aartech-dev/slot-car-track-mapper/electronics/electronics.kicad_sch

## KiCad design electronics/electronics.kicad_sch (2026-09-03)

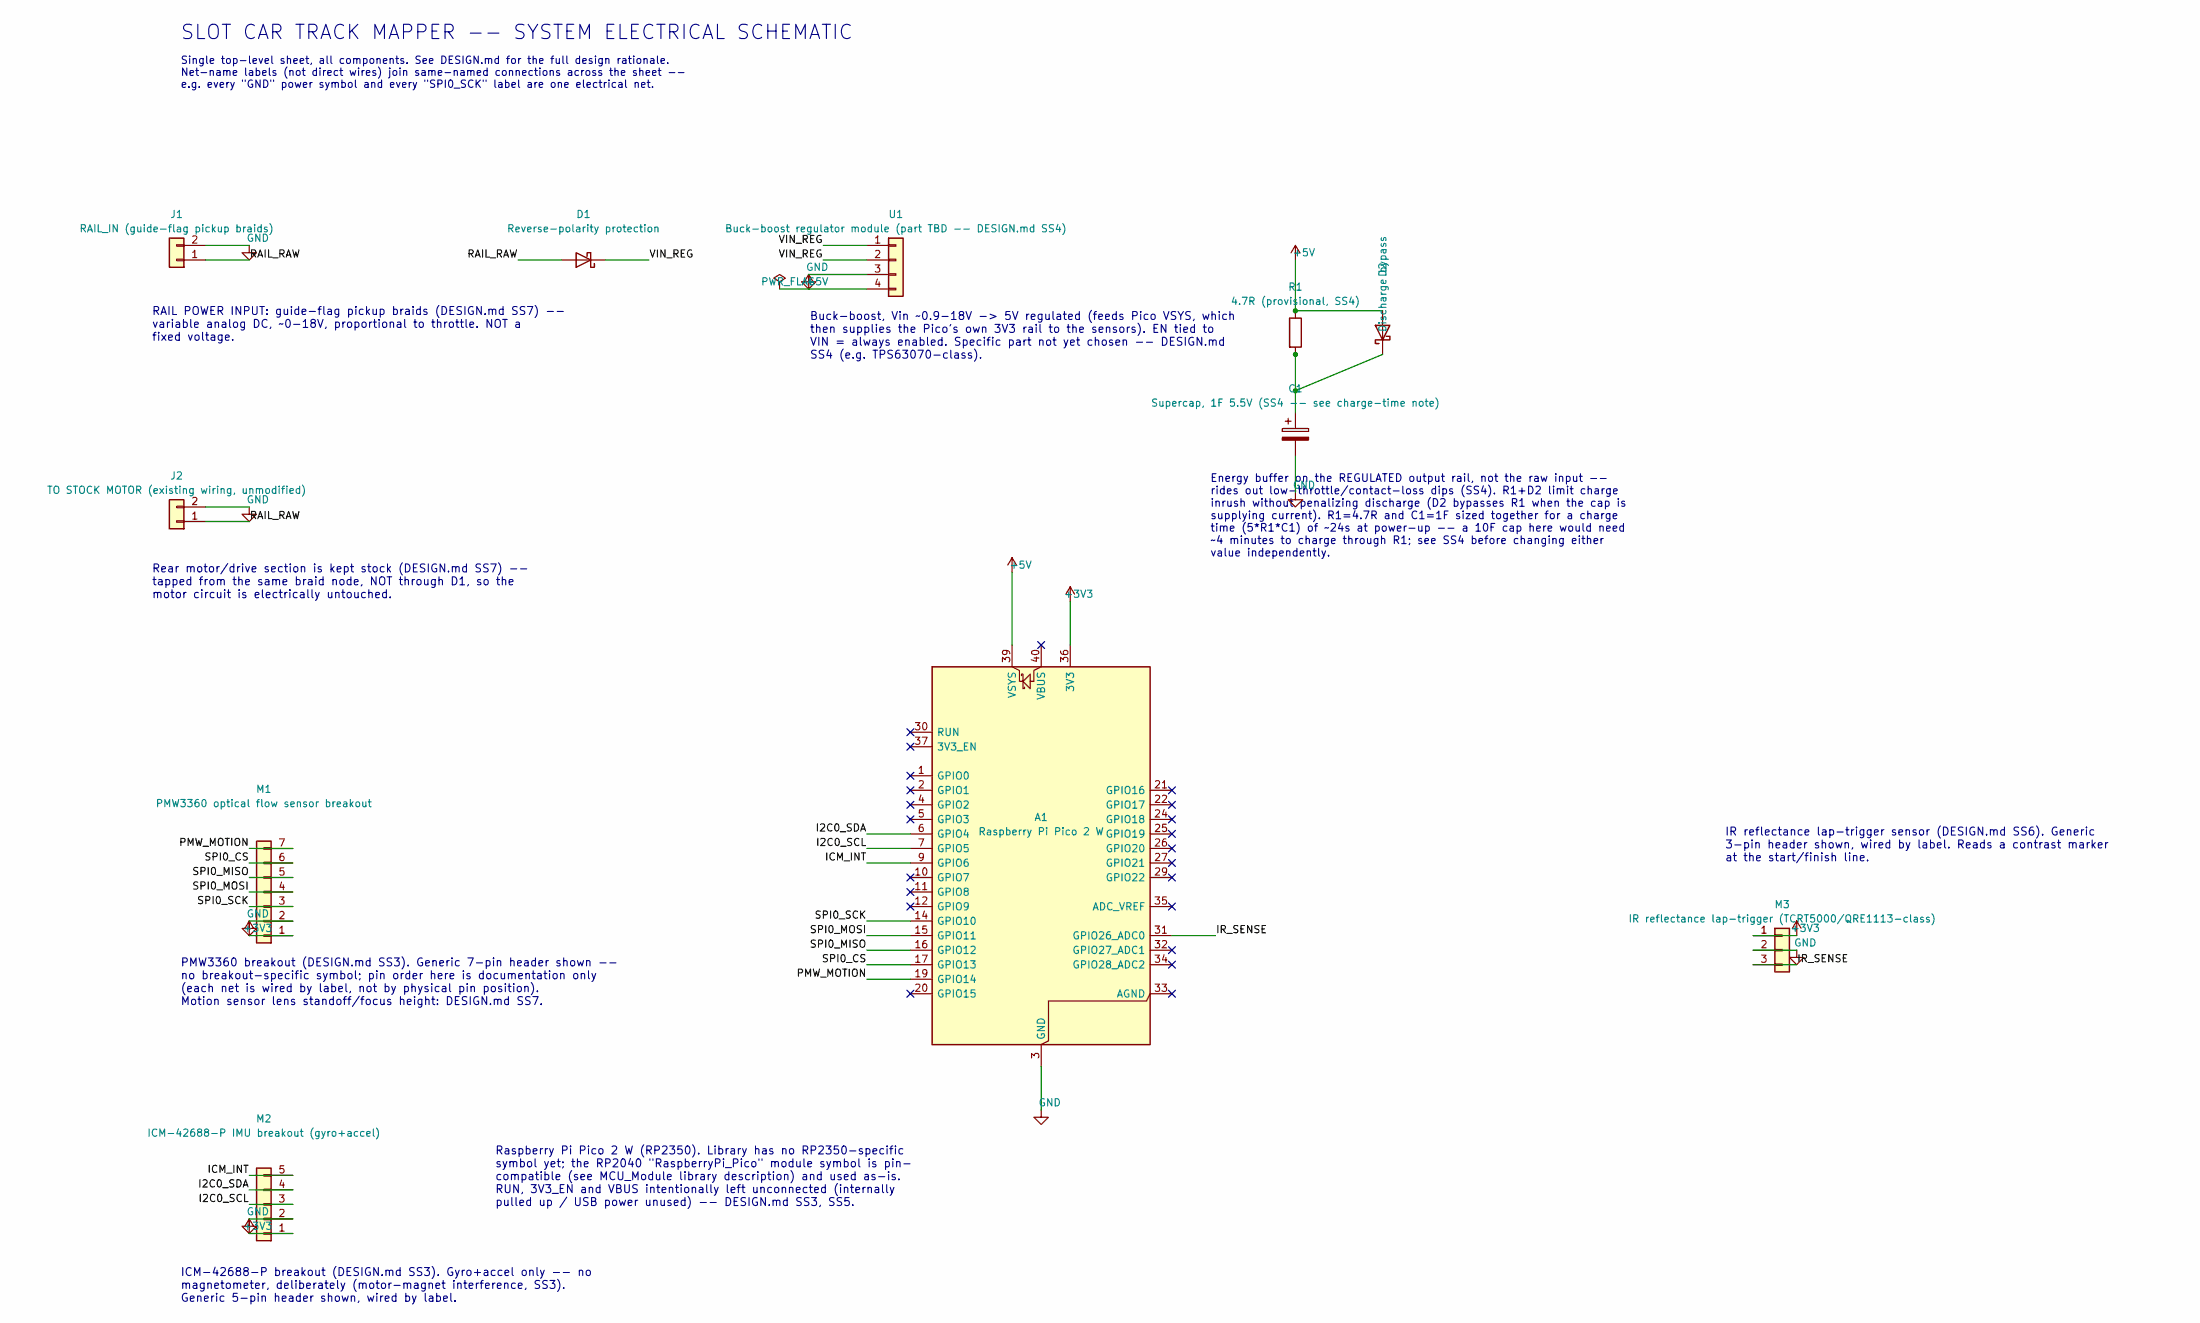
[picture p7: schematic electronics.kicad_sch]

Parts:
A1: Raspberry Pi Pico 2 W
C1: Supercap, 1F 5.5V (SS4 -- see charge-time note)
D1: Reverse-polarity protection
D2: Discharge bypass
J1: RAIL_IN (guide-flag pickup braids)
J2: TO STOCK MOTOR (existing wiring, unmodified)
M1: PMW3360 optical flow sensor breakout
M2: ICM-42688-P IMU breakout (gyro+accel)
M3: IR reflectance lap-trigger (TCRT5000/QRE1113-clas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
R1: 4.7R (provisional, SS4)
U1: Buck-boost regulator module (part TBD -- DESIGN.m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

Connections:
+3V3: A1.36 (3V3), M1.1, M2.1, M3.1
+5V: A1.39 (VSYS), D2.2 (A), R1.1, U1.4
GND: A1.3 (GND), A1.8 (GND), A1.13 (GND), A1.18 (GND), A1.23 (GND), A1.28 (GND), A1.38 (GND), C1.2, J1.2, J2.2, M1.2, M2.2, M3.2, U1.3
I2C0_SCL: A1.7 (GPIO5), M2.3
I2C0_SDA: A1.6 (GPIO4), M2.4
ICM_INT: A1.9 (GPIO6), M2.5
IR_SENSE: A1.31 (GPIO26_ADC0), M3.3
unnamed: C1.1, D2.1 (K), R1.2
PMW_MOTION: A1.19 (GPIO14), M1.7
RAIL_RAW: D1.2 (A), J1.1, J2.1
SPI0_CS: A1.17 (GPIO13), M1.6
SPI0_MISO: A1.16 (GPIO12), M1.5
SPI0_MOSI: A1.15 (GPIO11), M1.4
SPI0_SCK: A1.14 (GPIO10), M1.3
VIN_REG: D1.1 (K), U1.1, U1.2

Notes on the sheet:
Raspberry Pi Pico 2 W (RP2350). Library has no RP2350-specific symbol yet; the RP2040 "RaspberryPi_Pico" module symbol is pin- compatible (see MCU_Module library description) and used as-is. RUN, 3V3_EN and VBUS intentionally left unconnected (internally pulled up / USB power unused) -- DESIGN.md S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
RAIL POWER INPUT: guide-flag pickup braids (DESIGN.md SS7) -- variable analog DC, ~0-18V, proportional to throttle. NOT a fixed voltage.
Rear motor/drive section is kept stock (DESIGN.md SS7) -- tapped from the same braid node, NOT through D1, so the motor circuit is electrically untouched.
Buck-boost, Vin ~0.9-18V -> 5V regulated (feeds Pico VSYS, which then supplies the Pico's own 3V3 rail to the sensors). EN tied to VIN = always enabled. Specific part not yet chosen -- DESIGN.md SS4 (e.g. TPS63070-class).
Energy buffer on the REGULATED output rail, not the raw input -- rides out low-throttle/contact-loss dips (SS4). R1+D2 limit charge inrush without penalizing discharge (D2 bypasses R1 when the cap is supplying current). R1=4.7R and C1=1F sized together for a charge time (5*R1*C1) of ~24s at power-u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
PMW3360 breakout (DESIGN.md SS3). Generic 7-pin header shown -- no breakout-specific symbol; pin order here is documentation only (each net is wired by label, not by physical pin position). Motion sensor lens standoff/focus height: DESIGN.md SS7.
ICM-42688-P breakout (DESIGN.md SS3). Gyro+accel only -- no magnetometer, deliberately (motor-magnet interference, SS3). Generic 5-pin header shown, wired by label.
IR reflectance lap-trigger sensor (DESIGN.md SS6). Generic 3-pin header shown, wired by label. Reads a contrast marker at the start/finish line.
SLOT CAR TRACK MAPPER -- SYSTEM ELECTRICAL SCHEMATIC
Single top-level sheet, all components. See DESIGN.md for the full design rationale. Net-name labels (not direct wires) join same-named connections across the sheet -- e.g. every "GND" power symbol and every "SPI0_SCK" label are one electrical net.
